iz2k/splitFlapClockRadio/hw/pcb/splitFlapClockRadio_3D_Image.png

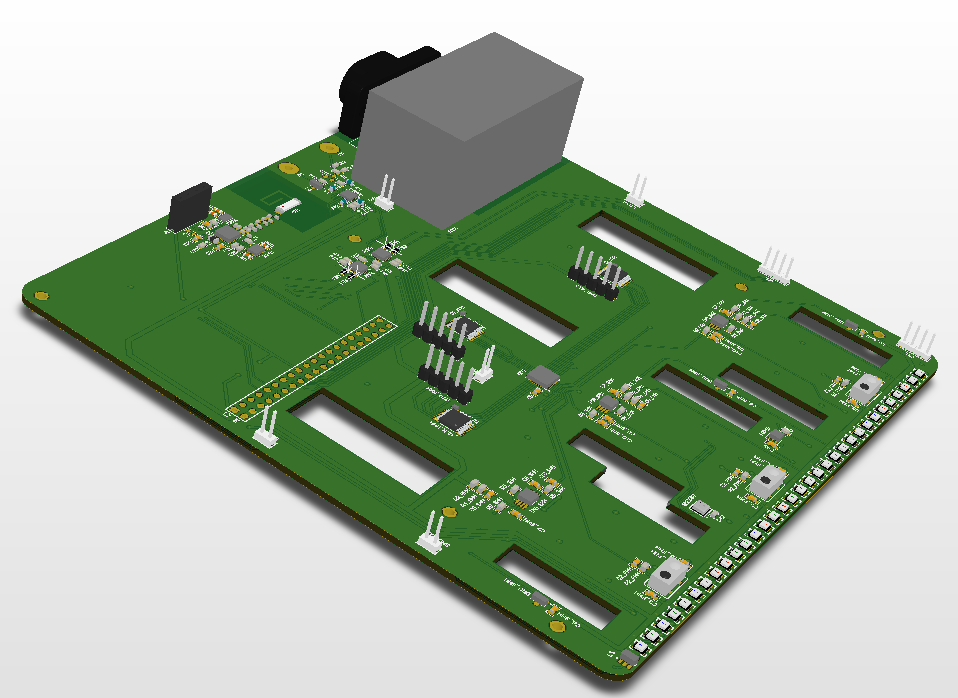
hw/pcb/splitFlapClockRadio_3D_Image.png
