iz2k/splitFlapClockRadio/3d/outputs/ui_Control_Wheel.stl

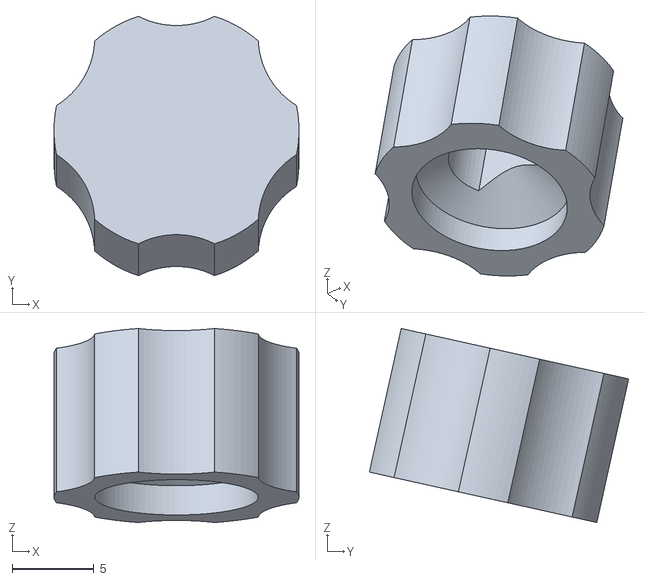
[picture p16: CAD file, 2021-02-09]
3d/outputs/ui_Control_Wheel.stl
15.0 x 15.9 x 11.9
