iz2k/splitFlapClockRadio/3d/outputs/footer.stl

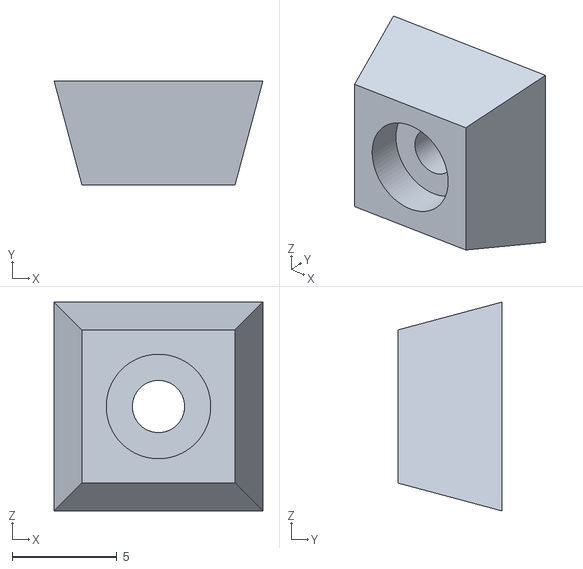
[picture p17: CAD file, 2021-02-09]
3d/outputs/footer.stl
10.0 x 5.00 x 10.0
