iz2k/splitFlapClockRadio/3d/outputs/gear-axle.stl

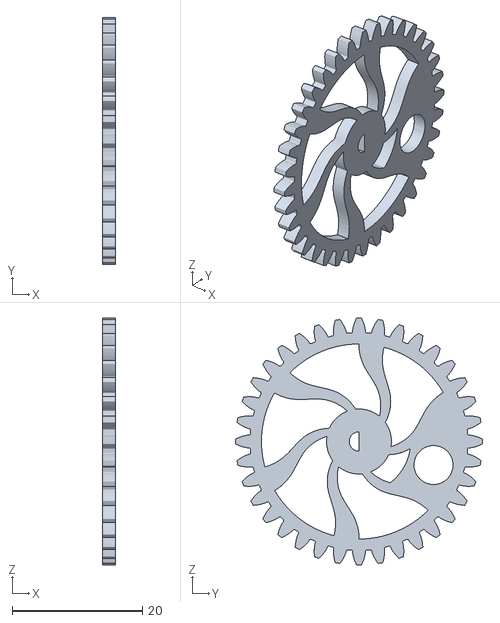
[picture p18: CAD file, 2021-02-09]
3d/outputs/gear-axle.stl
2.00 x 38.0 x 38.0
