iz2k/splitFlapClockRadio/sw/pyBackend/splitFlapClockRadioBackend/clock/clockWebRoutes.py

from flask import request as flask_request

from splitFlapClockRadioBackend.__main__ import App
from splitFlapClockRadioBackend.tools.jsonTools import prettyJson
from splitFlapClockRadioBackend.tools.timeTools import getDateTime



def defineClockWebRoutes(app: App):

    @app.webserver.flaskApp.route('/rest/clock/get-time', methods=['GET'])
    def getTime():
        return prettyJson(getDateTime(app.config.params['clock']['timeZone']))

    @app.webserver.flaskApp.route('/rest/clock/set-timezone', methods=['POST'])
    def setTimezone():
        content = flask_request.get_json(silent=True)
        if (content != None):
            app.config.updateClockParam('timeZone', content['nameValue'])
        return prettyJson({'status' : 'Timezone modified!'})

    @app.webserver.flaskApp.route('/rest/clock/get-mode', methods=['GET'])
    def getClockMode():
        return prettyJson(app.clock.mode)

    # /url?arg1=xxxx&arg2=yyy
    @app.webserver.flaskApp.route('/rest/clock/set-mode', methods=['GET'])
    def setClockMode():
        try:
            # Get arguments
            for parameter in flask_request.args:
                value = flask_request.args.get(parameter)
                # Update mode parameter
                if(parameter == 'mode'):
                    app.clock.mode = value
            return prettyJson(app.clock.mode)
        except Exception as e:
            print(e)
            return 'Invalid parameters'

    # /url?arg1=xxxx&arg2=yyy
    @app.webserver.flaskApp.route('/rest/clock/get-flap-status', methods=['GET'])
    def getFlapStatus():
        try:
            return prettyJson(app.clock.smbus430.getFlapStatus(flask_request.args['type']))
        except Exception as e:
            print(e)
            return 'Invalid parameters. Please specify type=hh, mm or ww'

    # /url?arg1=xxxx&arg2=yyy
    @app.webserver.flaskApp.route('/rest/clock/set-flap-parameter', methods=['GET'])
    def setFlapParameter():
        try:
            return prettyJson(app.clock.smbus430.setFlapParameter(flask_request.args['type'], flask_request.args['parameter'], int(flask_request.args['value'])))
        except Exception as e:
            print(e)
            return 'Invalid parameters. Please specify type=hh, mm or ww'
