iz2k/splitFlapClockRadio/sw/pyBackend/splitFlapClockRadioBackend/clock/smbus430/smbusMsp430.py

import time
from datetime import datetime
from enum import Enum

import pigpio
import smbus
from termcolor import colored

from splitFlapClockRadioBackend.clock.smbus430.typedef import SMBUS_OPS, MSP430_REGS, FLAP_REGS, FLAP_IDX
from splitFlapClockRadioBackend.tools.menuTools import getKeyFromDictionarySubitemName, select_value, doReturn, doMenu


class smbusMsp430:

    class HW(Enum):
        I2C_ADDRESS=0x16
        RST_GPIO = 12

    def __init__(self, SMBusChannel=1, i2cAddress=0x16, skipReset=False):
        self.bus = smbus.SMBus(SMBusChannel)
        self.i2c_address = i2cAddress

        self.pi = pigpio.pi()

        if not skipReset:
            # Reset the device
            self.pi.set_mode(self.HW.RST_GPIO.value, pigpio.OUTPUT)
            self.pi.write(self.HW.RST_GPIO.value, 0)
            time.sleep(0.1)
            self.pi.write(self.HW.RST_GPIO.value, 1)
            #self.pi.set_mode(self.HW.RST_GPIO.value, pigpio.INPUT)

    def read_registerKey(self, key):
        data = self.bus.read_i2c_block_data(self.i2c_address, int(key) + SMBUS_OPS['SMB_OP_READ'], MSP430_REGS[key]['len'])
        return int.from_bytes(data, byteorder='little')

    def write_registerKey(self, key, value):
        value_byte_array = value.to_bytes(MSP430_REGS[key]['len'], byteorder='little')
        self.bus.write_i2c_block_data(self.i2c_address, int(key) + SMBUS_OPS['SMB_OP_WRITE'], [b for b in value_byte_array])

    def getKeyFromRegisterName(self, name):
        for reg in MSP430_REGS:
            if MSP430_REGS[reg]['name'] == name:
                return reg

    def read_registerName(self, name):
        return self.read_registerKey(self.getKeyFromRegisterName(name))

    def write_registerName(self, name, value):
        return self.write_registerKey(self.getKeyFromRegisterName(name), value)

    ####    MENU IMPLEMENTATION ####
    def menu(self, preTitle):
        menuItems = {
            'title': preTitle + ' >> MSP430',
            'options': {
                '1': {'descriptor': 'Read all registers', 'function': self.readAllRegisters},
                '2': {'descriptor': 'Write register', 'function': self.writeRegister},
                '3': {'descriptor': 'Set current time', 'function': self.setCurrentTime},
                'r': {'descriptor': 'return', 'function': doReturn},
            }
        }

        # Loop on menu
        run = True
        while run:
            run = doMenu(menuItems)
        return True

    def readAllRegisters(self,preTitle):
        print(colored(preTitle + ' >> Reading all registers', 'magenta'))
        for reg in MSP430_REGS:
            print ('\t* ' + MSP430_REGS[reg]['name'] + ' = ' + self.show_reg(reg))
        return True

    def show_reg(self, reg):
        raw = self.read_registerKey(reg)
        if MSP430_REGS[reg]['type'] is int:
            return str(raw)
        if MSP430_REGS[reg]['type'] is 'msp43xFwVersion':
            major = raw >> 8
            minor = raw & 0xFF
            return str(major) + '.' + str(minor)
        if isinstance(MSP430_REGS[reg]['type'],dict):
            return MSP430_REGS[reg]['type'][str(raw)]

    def writeRegister(self,preTitle):
        print(colored(preTitle + ' >> Writing specific register', 'magenta'))
        key = getKeyFromDictionarySubitemName(MSP430_REGS)
        if key == None:
            return True
        value = select_value(MSP430_REGS[key])
        if value == None:
            return True
        self.write_registerKey(key, int(value))
        return True

    def setCurrentTime(self, preTitle):
        curTime = datetime.now()
        print(colored(preTitle + ' >> Setting current time: ' + str(curTime.hour).zfill(2) + ':' + str(curTime.minute).zfill(2), 'magenta'))
        self.write_registerKey(self.getKeyFromRegisterName('hh_desired_digit'), curTime.hour)
        self.write_registerKey(self.getKeyFromRegisterName('mm_desired_digit'), curTime.minute)

    def getFlapStatus(self, idx):
        status = {'FLAP_TYPE': FLAP_IDX[idx]}
        for reg in FLAP_REGS[idx]:
            status[reg] = self.show_reg(FLAP_REGS[idx][reg])
        return status

    def setFlapParameter(self, idx, param, value):
        self.write_registerKey(FLAP_REGS[idx][param], value)
        return self.getFlapStatus(idx)
