iz2k/splitFlapClockRadio/fw/msp430_flapCtl/smbus/smbusSlave.h

/*
 * i2c-slave.h
 *
 *  Created on: 24 abr. 2020
 *      Author: IbonZalbide
 */

#ifndef DRIVERS_SMBUS_SLAVE_H_
#define DRIVERS_SMBUS_SLAVE_H_

#include <stdint.h>

#define I2C_BUFFER_LENGTH 6
#define I2C_SLAVE_ADDR 0x16

#define MAX_SMB_REGS 32


typedef enum{
    SMB_OP_NONE     = 0b00000000,
    SMB_OP_READ     = 0b01000000,
    SMB_OP_WRITE    = 0b10000000,
    SMB_OP_MASK     = 0b11000000
} smbusOperation;

typedef enum i2cStateMachine{
    IDLE_MODE,
    NACK_MODE,
    TX_REG_ADDRESS_MODE,
    RX_REG_ADDRESS_MODE,
    TX_DATA_MODE,
    RX_DATA_MODE,
    SWITCH_TO_RX_MODE,
    SWITHC_TO_TX_MODE,
    TIMEOUT_MODE
} i2cStateMachine;

struct SmbusRegister
{
    uint8_t smbusAddress;
    void * mcuAddress;
    uint8_t length;
};

void initSmbusSlave();

void I2C_Slave_ProcessCMD(uint8_t cmd);
void I2C_Slave_TransactionDone(uint8_t cmd);
void CopyArray(uint8_t *source, uint8_t *dest, uint8_t count);

void addSmbusRegister(SmbusRegister);
uint8_t* getRegPointer(uint8_t);
uint8_t getRegLength(uint8_t);


#endif /* DRIVERS_SMBUS_SLAVE_H_ */
